KAZOOSH/solarbird/circuit/Solaranimal210527_2049/SolaranimalCircuit.png

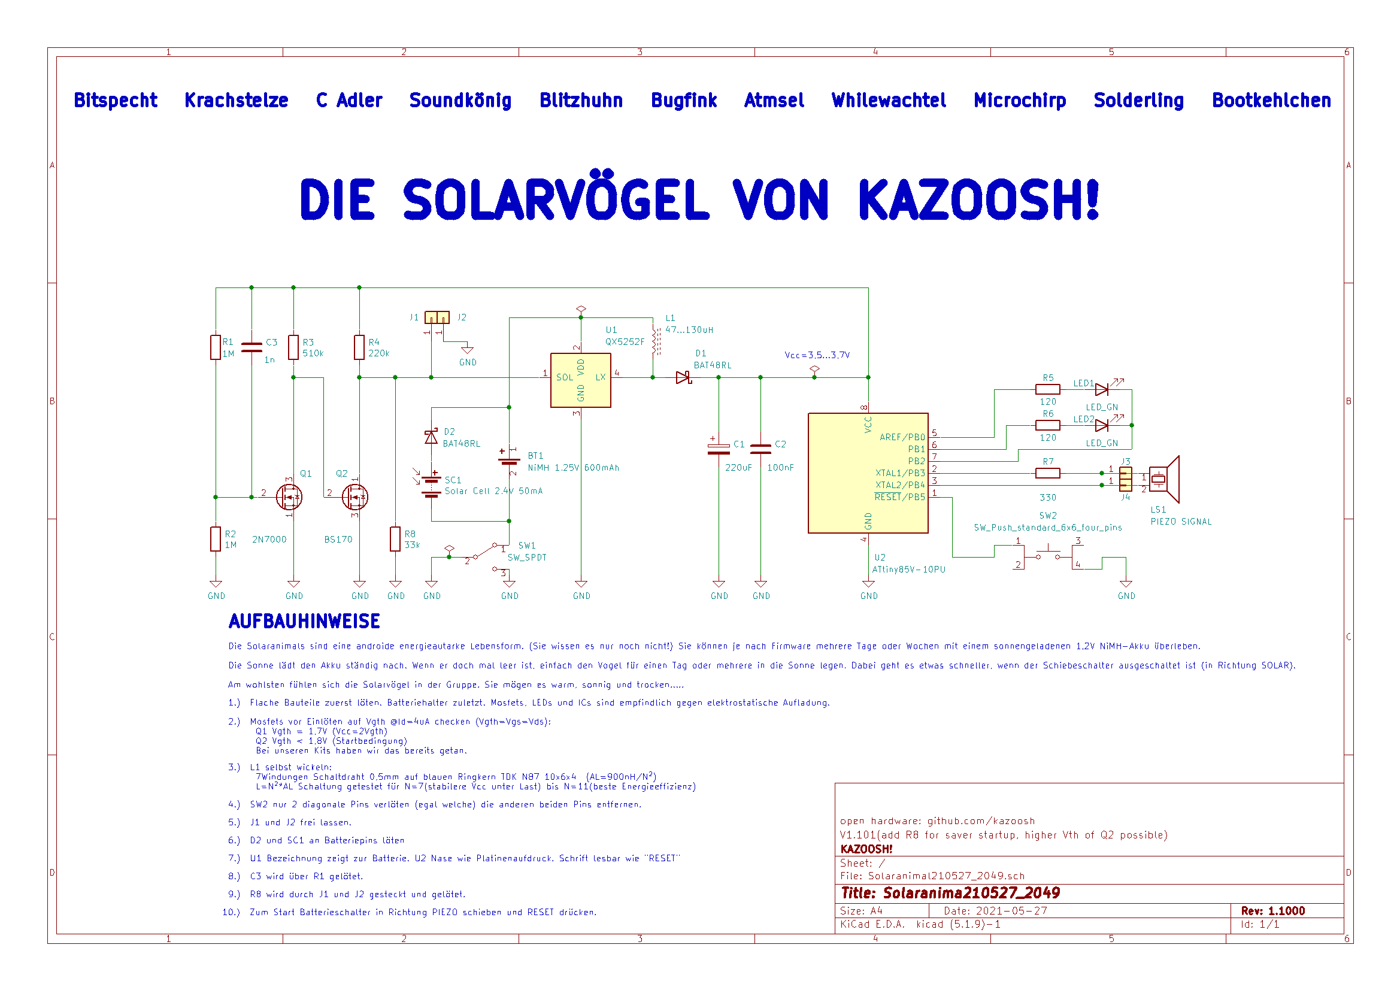
circuit/Solaranimal210527_2049/SolaranimalCircuit.png
