KAZOOSH/solarbird/circuit/spice/circuit.png

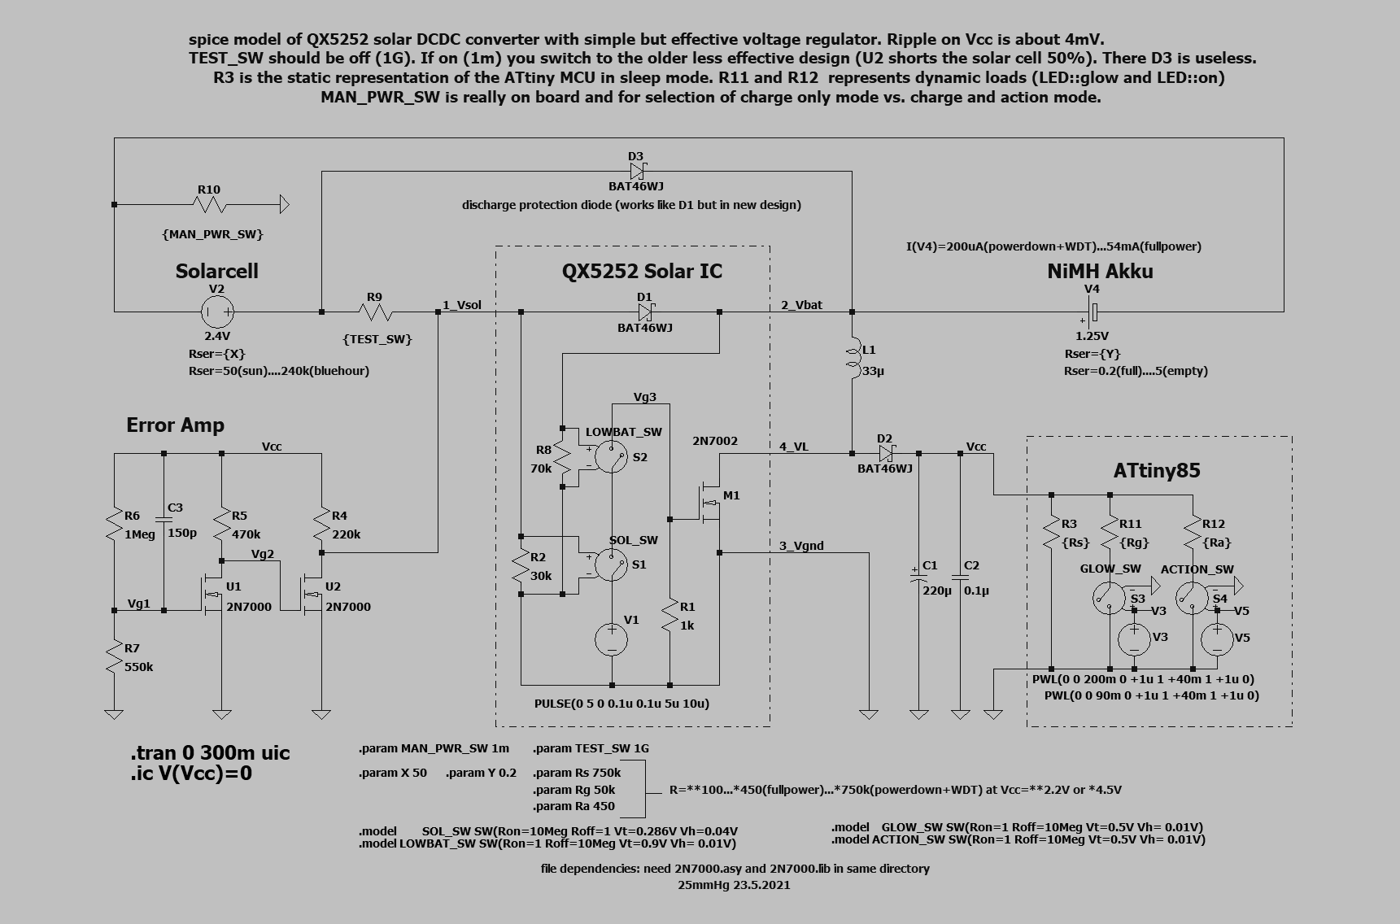
circuit/spice/circuit.png
