KAZOOSH/solarbird/pcb/Solaranimal_current pcb/board_b.png

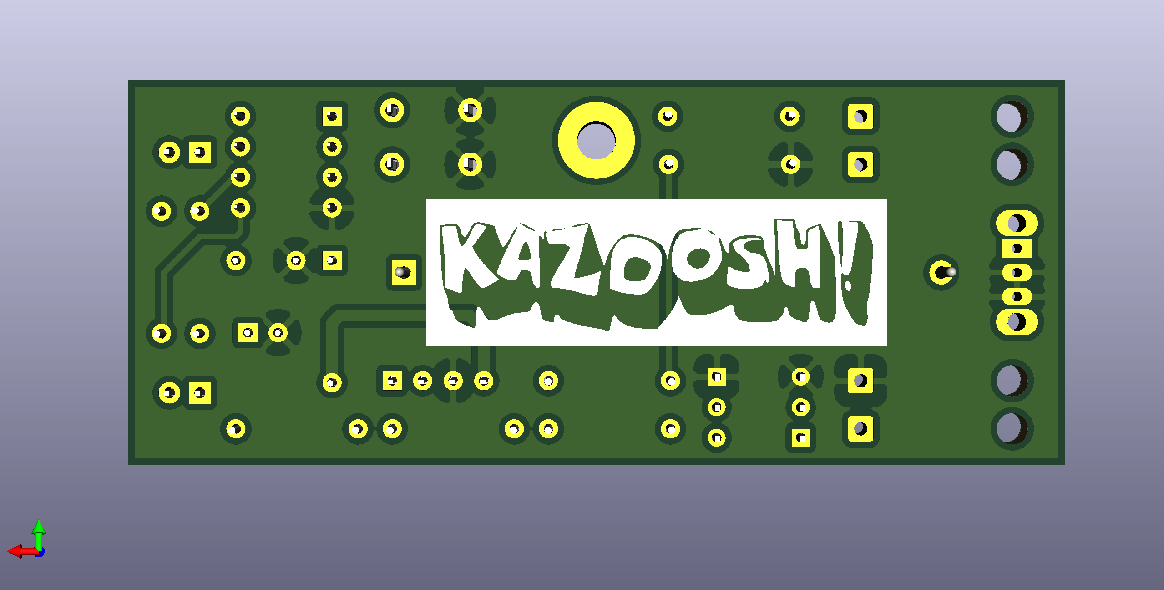
pcb/Solaranimal_current pcb/board_b.png
