KAZOOSH/solarbird/pcb/Solaranimal_current pcb/board_f.png

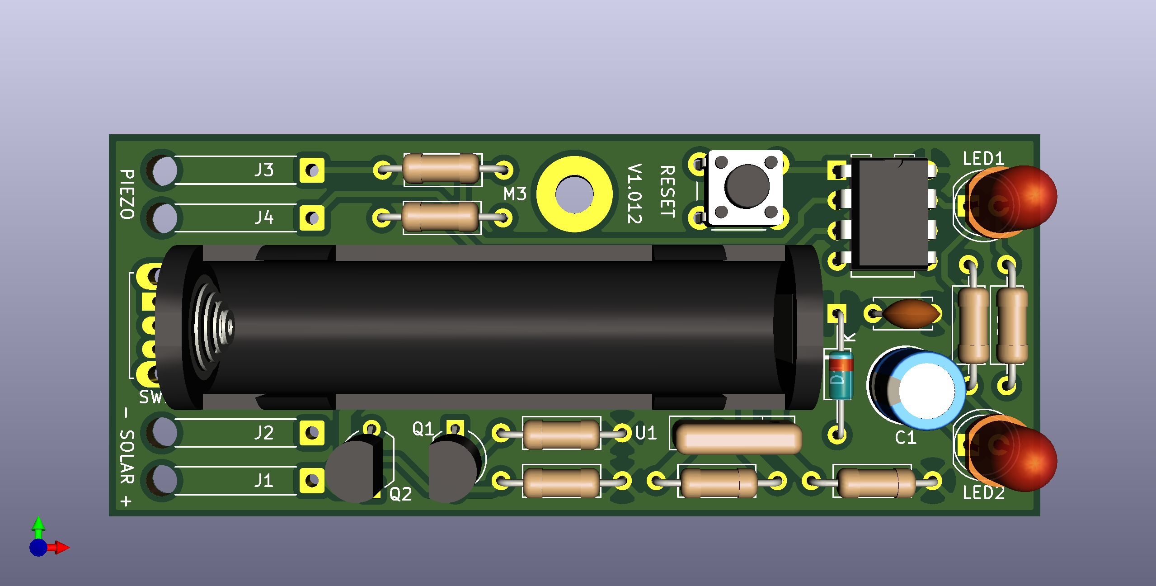
pcb/Solaranimal_current pcb/board_f.png
