KAZOOSH/solarbird/pcb/Solaranimal_current pcb/board_s.png

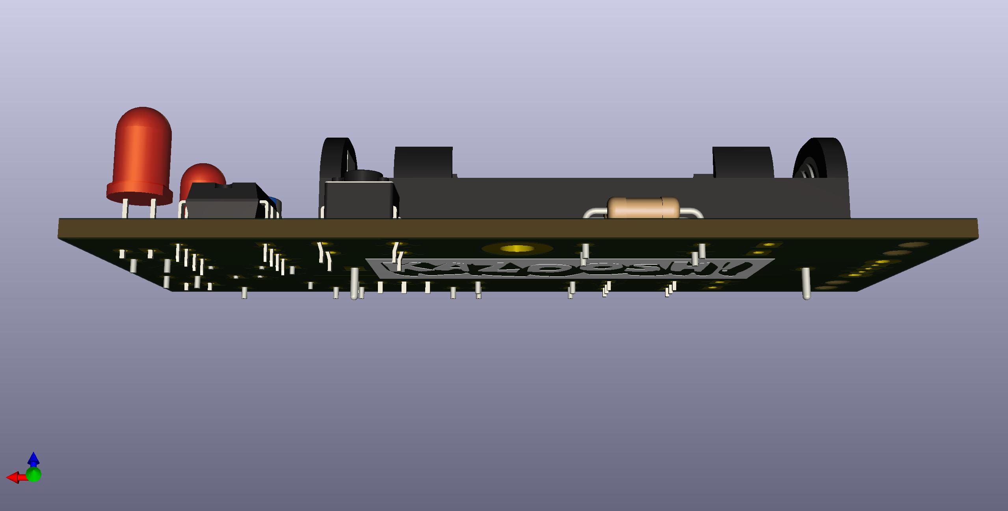
pcb/Solaranimal_current pcb/board_s.png
