KAZOOSH/solarbird/pcb/Solaranimal_current pcb/circuit.png

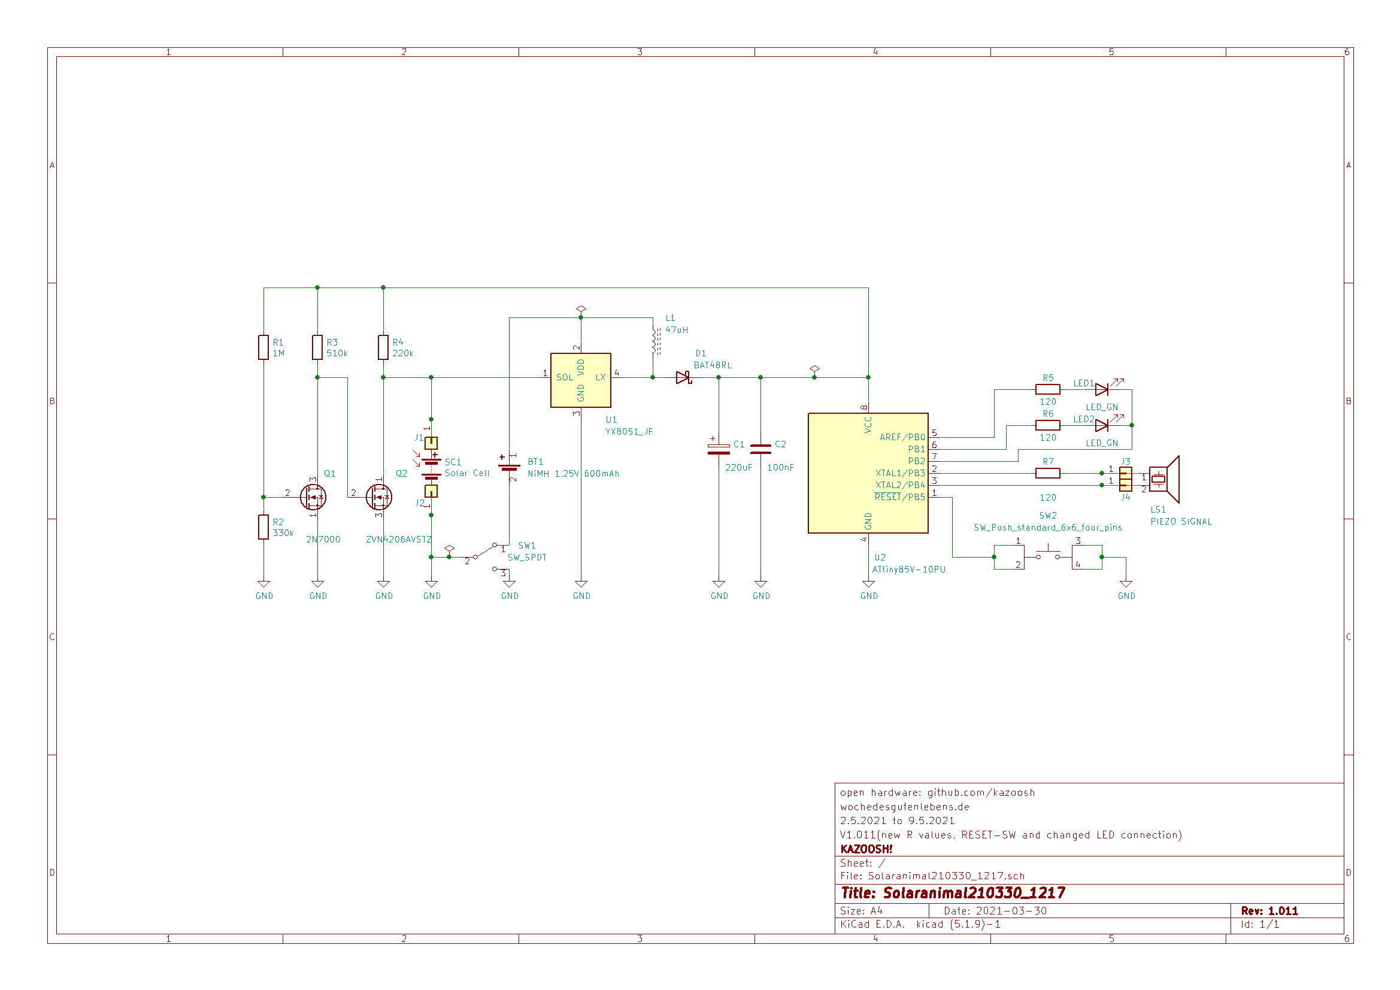
pcb/Solaranimal_current pcb/circuit.png
