KAZOOSH/solarbird/pcb/Solaranimal_current pcb/dimensions.png

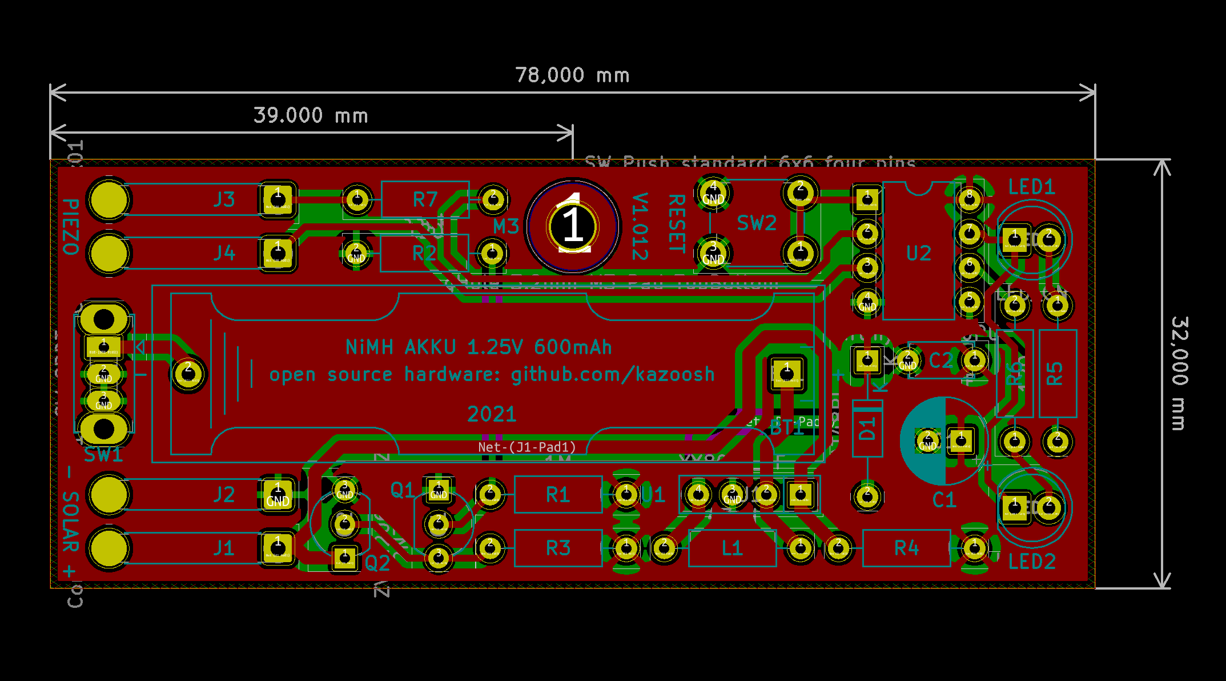
pcb/Solaranimal_current pcb/dimensions.png
