KAZOOSH/solarbird/material/capsense.png

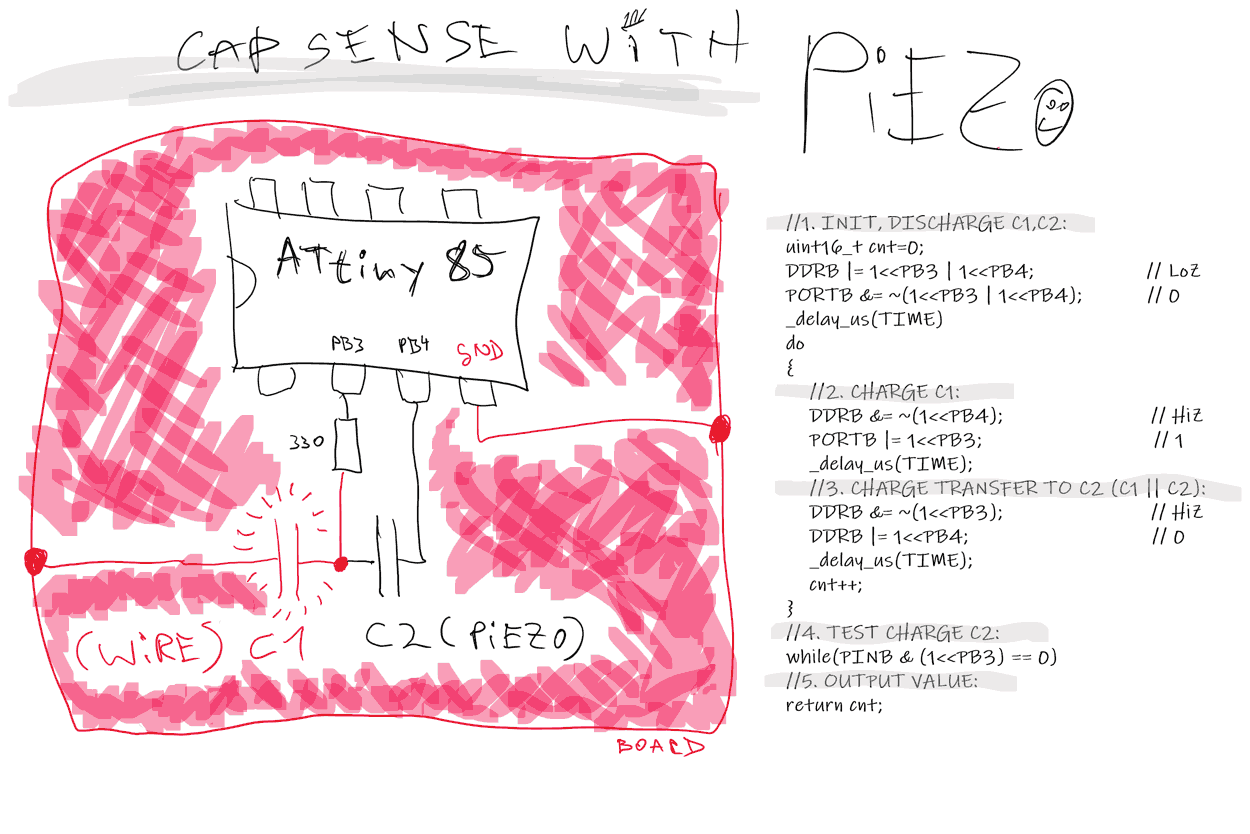
material/capsense.png
