KAZOOSH/solarbird/material/cicadas_waves/1_cicadas_envelope.jpg

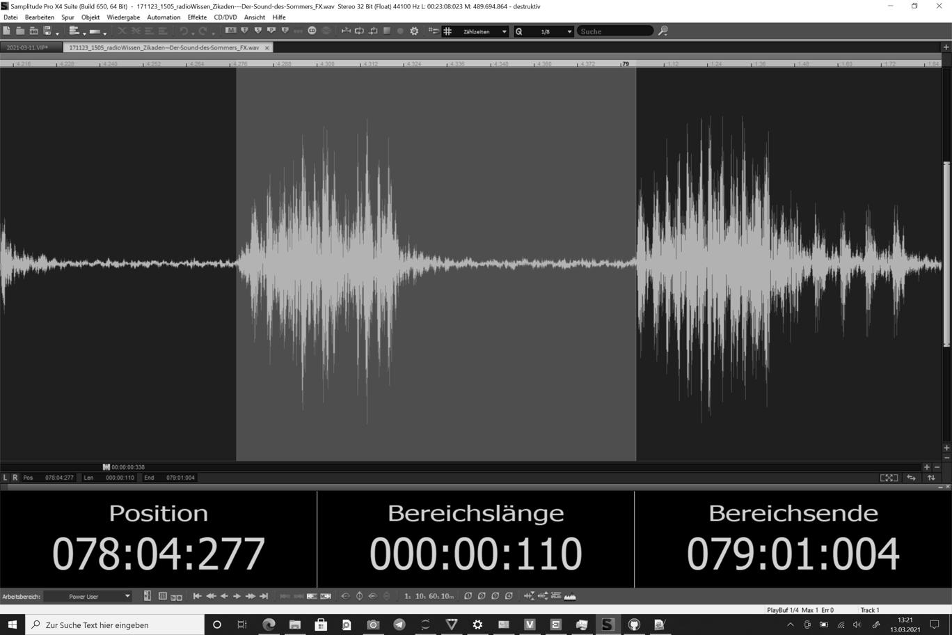
material/cicadas_waves/1_cicadas_envelope.jpg
