KAZOOSH/solarbird/material/cicadas_waves/2_cicadas_envelope_detail.jpg

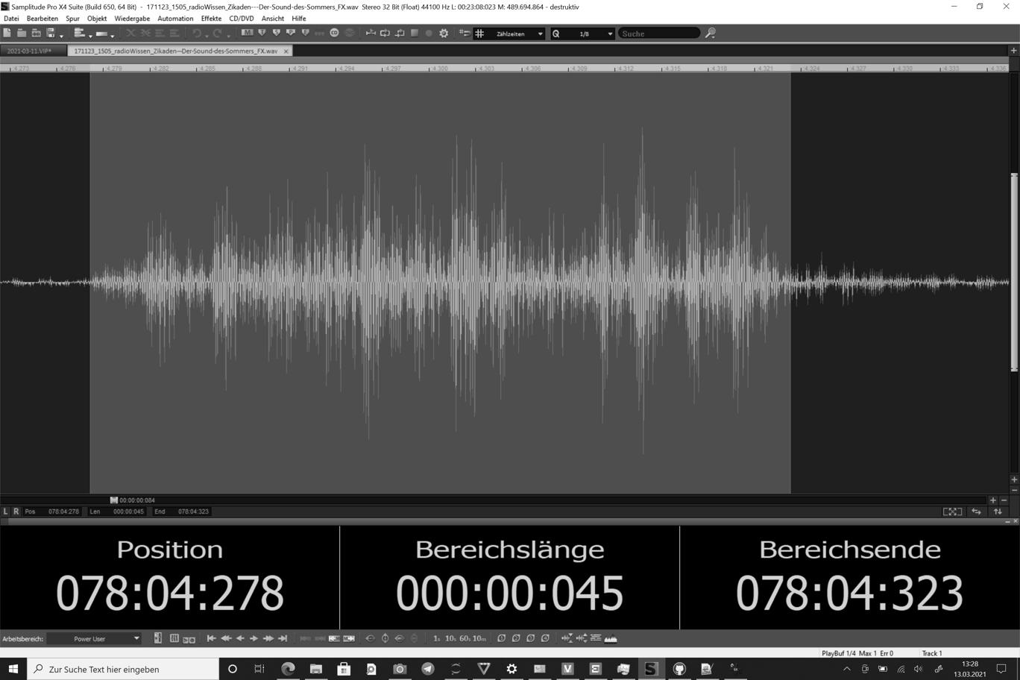
material/cicadas_waves/2_cicadas_envelope_detail.jpg
