KAZOOSH/solarbird/material/cicadas_waves/3_cicadas_3cycles.jpg

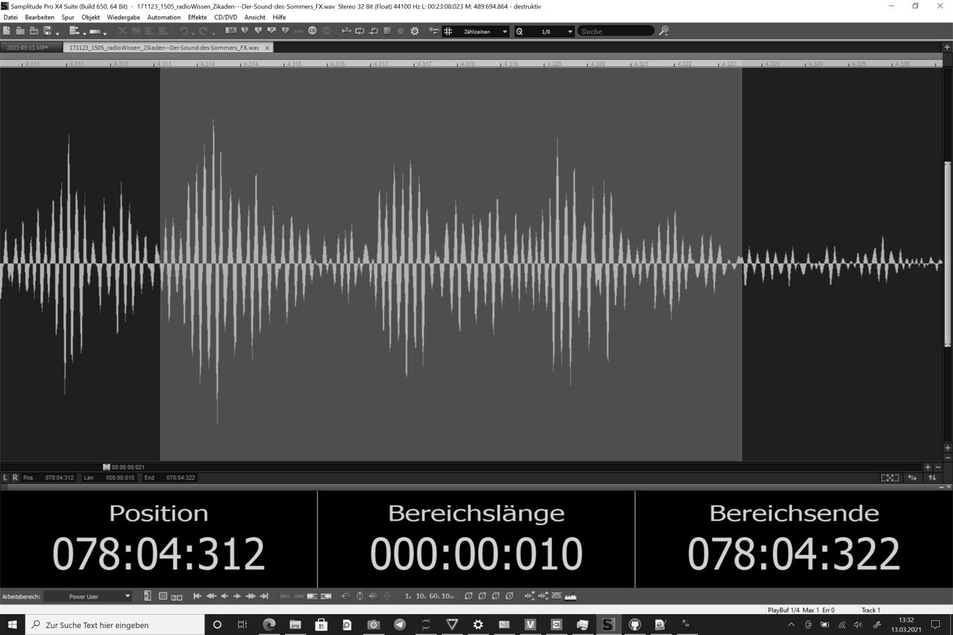
material/cicadas_waves/3_cicadas_3cycles.jpg
