KAZOOSH/solarbird/material/cicadas_waves/4_cicadas_cycle_with_samples.jpg

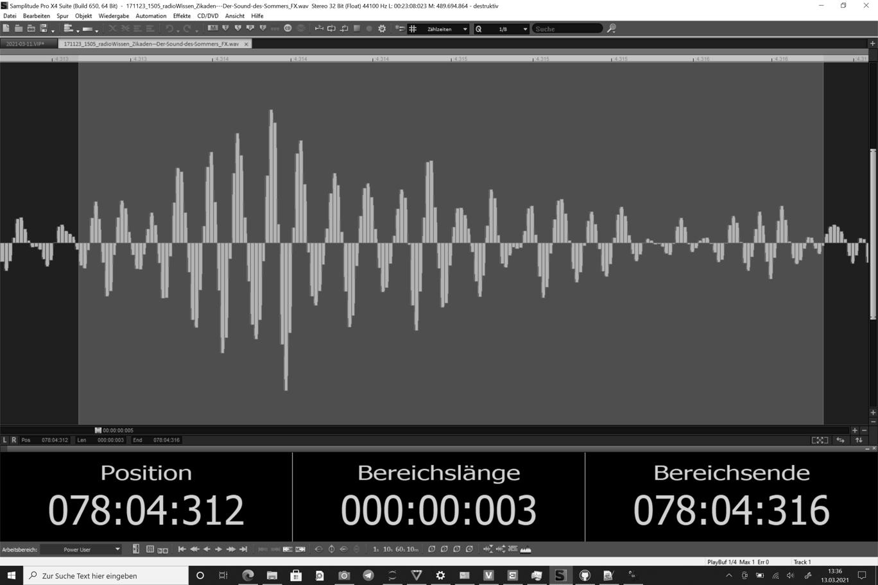
material/cicadas_waves/4_cicadas_cycle_with_samples.jpg
