KAZOOSH/solarbird/material/pwrsolution1.png

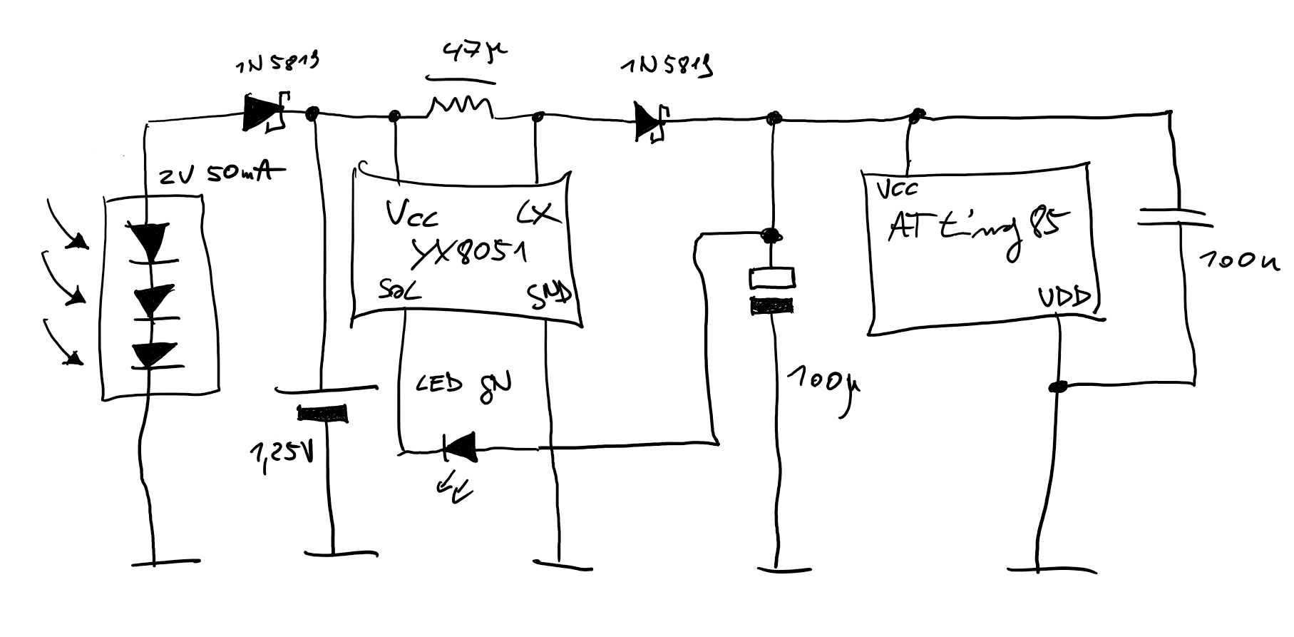
material/pwrsolution1.png
