KAZOOSH/solarbird/material/pwrsolution4.png

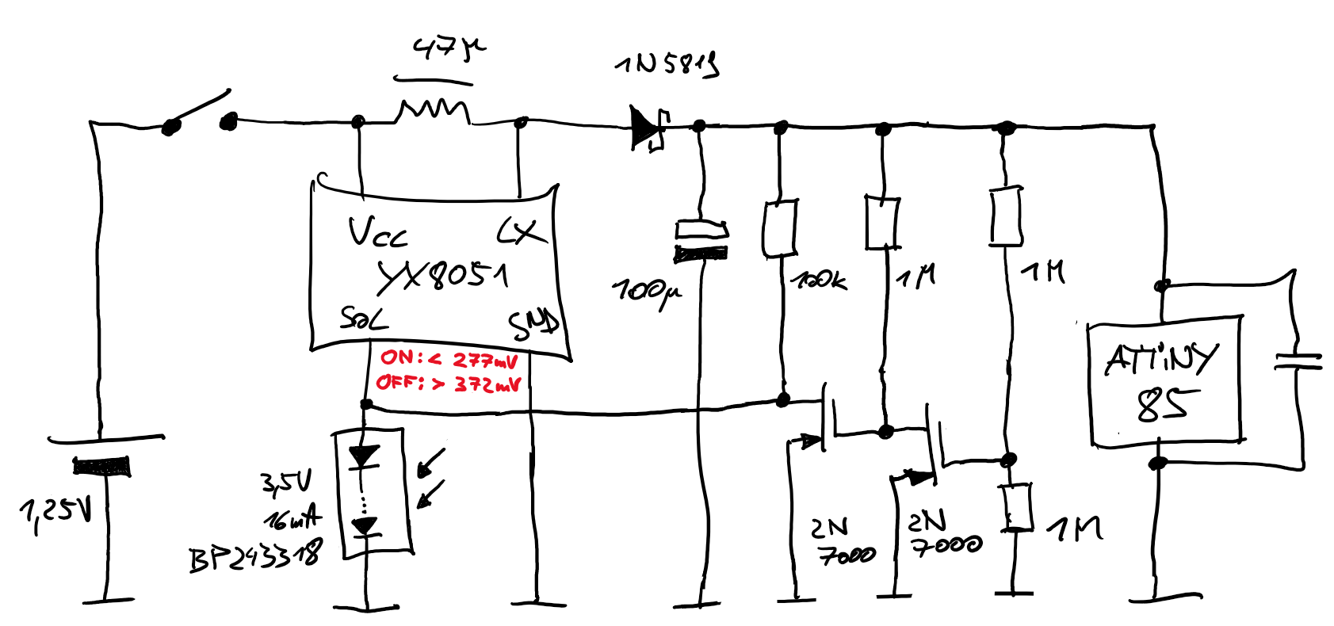
material/pwrsolution4.png
