KAZOOSH/solarbird/circuit/spice/ErrorAmpACDC.asc

C1: cap; {C}
R1: res; {R}
R2: res; 470k
R3: res; 1Meg
R4: res; 550k
R5: res; 30k
U1: 2N7000
U2: 2N7000
V2: voltage; AC 1
Named nets: 0, Vcc, Vg1, Vg2, out
Error Amp
.ac oct 12 0.1 1G
.op V(Vcc)=4.5V
.step param C list 0 33p 100p 330p
.dc V2 0 5
.step param R list 220k 270k 330k
inside
QX5252
