KAZOOSH/solarbird/circuit/spice/Solarbird.asc

C1: polcap; 220µ; V=4 Irms=3.72678 Rser=0.018 Lser=0 mfg="KEMET" pn="A700D107M004ATE018" type="Al electrolytic"
C2: cap; 0.1µ; V=16 Irms=4.39 Rser=0.0357547 Lser=0 mfg="KEMET" pn="C0402C104K4RAC" type="X7R"
C3: cap; 150p
D1: schottky; BAT46WJ
D2: schottky; BAT46WJ
D3: schottky; BAT46WJ
L1: ind; 33µ; Rser=0.01
M1: nmos; 2N7002
R1: res; 1k
R2: res; 30k
R3: res; {Rs}
R4: res; 220k
R5: res; 470k
R6: res; 1Meg
R7: res; 550k
R8: res; 70k
R9: res; {TEST_SW}
R10: res; {MAN_PWR_SW}
R11: res; {Rg}
R12: res; {Ra}
S1: sw; SOL_SW
S2: sw; LOWBAT_SW
S3: sw; GLOW_SW
S4: sw; ACTION_SW
U1: 2N7000
U2: 2N7000
V1: voltage; PULSE(0 5 0 0.1u 0.1u 5u 10u)
V2: voltage; 2.4V; Rser={X}
V3: voltage; PWL(0 0 200m 0 +1u 1 +40m 1 +1u 0)
V4: cell; 1.25V; Rser={Y}
V5: voltage; PWL(0 0 90m 0 +1u 1 +40m 1 +1u 0)
Named nets: 2_Vbat, 4_VL, 1_Vsol, 3_Vgnd, 0, Vcc, Vg1, Vg2, Vg3, V3, V5
.model        SOL_SW SW(Ron=10Meg Roff=1 Vt=0.286V Vh=0.04V
QX5252 Solar IC
.tran 0 300m uic
.param X 50
NiMH Akku
Solarcell
ATtiny85
.ic V(Vcc)=0
.model LOWBAT_SW SW(Ron=1 Roff=10Meg Vt=0.9V Vh= 0.01V)
Rser=0.2(full)....5(empty)
Rser=50(sun)....240k(bluehour)
.param Y 0.2
.param Rs 750k
R=**100...*450(fullpower)...*750k(powerdown+WDT) at Vcc=**2.2V or *4.5V
I(V4)=200uA(powerdown+WDT)...54mA(fullpower)
.param MAN_PWR_SW 1m
.param TEST_SW 1G
spice model of QX5252 solar DCDC converter with simple but effective voltage regulator. Ripple on Vcc is about 4mV.
TEST_SW should be off (1G). If on (1m) you switch to the older less effective design (U2 shorts the solar cell 50%). There D3 is useless.                       
     R3 is the static representation of the ATtiny MCU in sleep mode. R11 and R12  represents dynamic loads (LED::glow and LED::on)
                           MAN_PWR_SW is really on board and for selection of charge only mode vs. charge and action mode.
discharge protection diode (works like D1 but in new design)
Error Amp
.param Rg 50k
.param Ra 450
.model    GLOW_SW SW(Ron=1 Roff=10Meg Vt=0.5V Vh= 0.01V)
.model ACTION_SW SW(Ron=1 Roff=10Meg Vt=0.5V Vh= 0.01V)
file dependencies: need 2N7000.asy and 2N7000.lib in same directory
25mmHg 23.5.2021
