KAZOOSH/solarbird/circuit/Solaranimal210527_2049/Solaranimal210527_2049.sch

## KiCad design circuit/Solaranimal210527_2049/Solaranimal210527_2049.sch (2021-06-29)

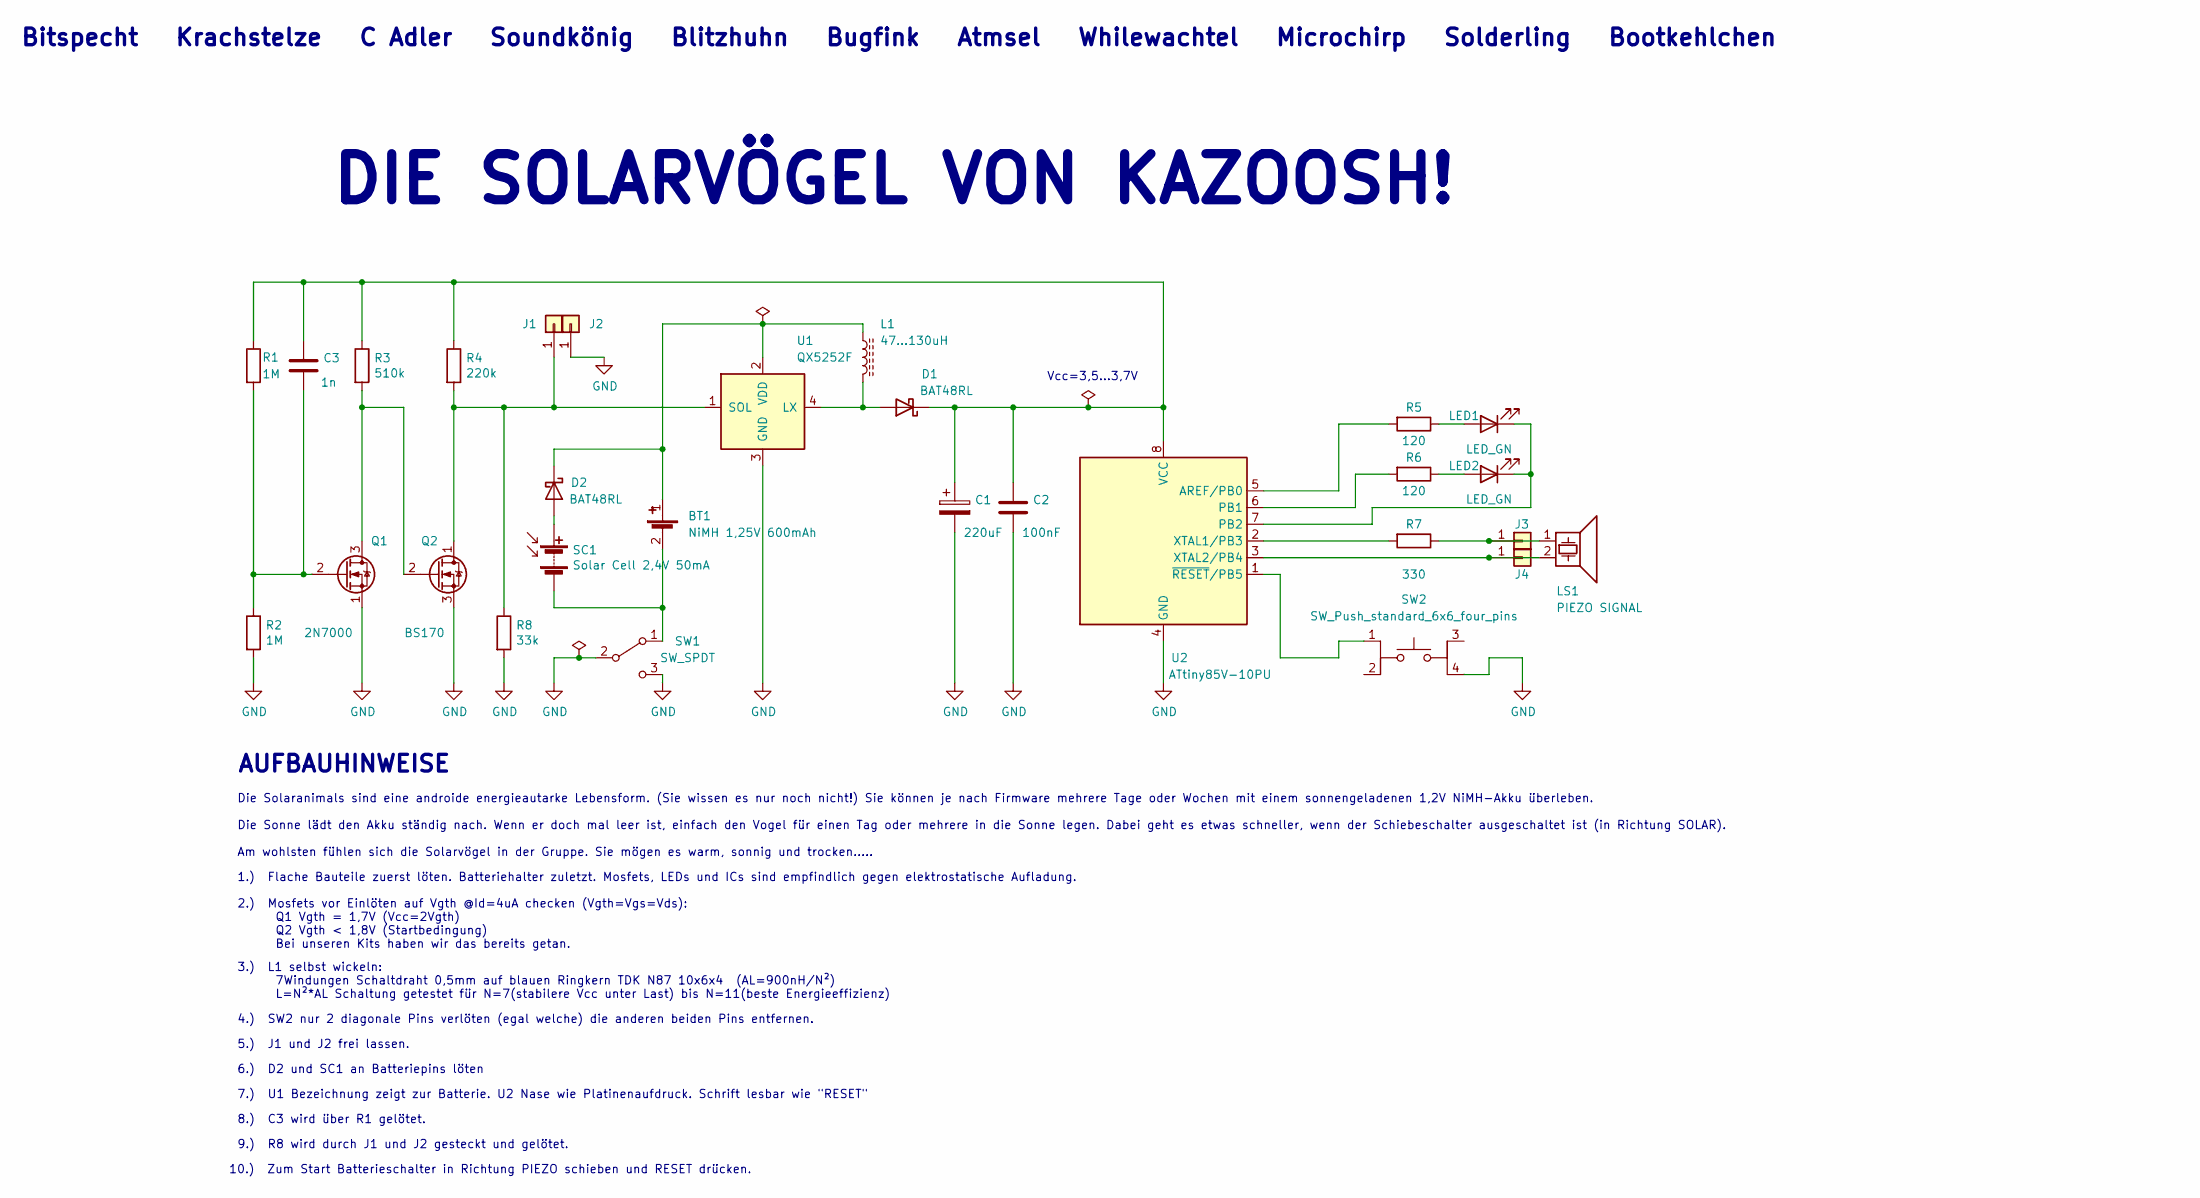
[picture p26: schematic Solaranimal210527_2049.sch]

Parts:
BT1: NiMH 1,25V 600mAh; BatteryHolder_Keystone_2466_1xAAA
C1: 220uF; CP_Radial_D6.3mm_P2.50mm
C2: 100nF; C_Disc_D4.7mm_W2.5mm_P5.00mm
C3: 1n; C_Disc_D4.7mm_W2.5mm_P5.00mm
D1, D2: BAT48RL; D_DO-35_SOD27_P10.16mm_Horizontal
J1, J2, J3, J4: Conn_01x01; SolderWire-0.5sqmm_1x01_D0.9mm_OD2.1mm_Relief
L1: 47...130uH; R_Axial_DIN0207_L6.3mm_D2.5mm_P10.16mm_Horizontal
LED1, LED2: LED_GN; LED_D5.0mm
LS1: PIEZO SIGNAL
Q1: 2N7000; TO-92_Inline_Wide
Q2: BS170; TO-92_Inline_Wide
R1, R2: 1M; R_Axial_DIN0207_L6.3mm_D2.5mm_P10.16mm_Horizontal
R3: 510k; R_Axial_DIN0207_L6.3mm_D2.5mm_P10.16mm_Horizontal
R4: 220k; R_Axial_DIN0207_L6.3mm_D2.5mm_P10.16mm_Horizontal
R5, R6: 120; R_Axial_DIN0207_L6.3mm_D2.5mm_P10.16mm_Horizontal
R7: 330; R_Axial_DIN0207_L6.3mm_D2.5mm_P10.16mm_Horizontal
R8: 33k; R_Axial_DIN0207_L6.3mm_D2.5mm_P10.16mm_Horizontal
SC1: Solar Cell 2,4V 50mA
SW1: SW_SPDT; SW_Slide_1P2T_CK_OS102011MS2Q
SW2: SW_Push_standard_6x6_four_pins; SW_PUSH_6mm_H5mm_4pin
U1: QX5252F
U2: ATtiny85V-10PU; DIP-8_W7.62mm

Connections:
GND: C1.2, C2.2, J2.1, Q1.1 (S), Q2.3 (S), R2.2, R8.2, SW1.2 (B), SW1.3 (C), SW2.4, U1.3 (GND), U2.4 (GND)
unnamed: BT1.1 (-), D2.1 (K), L1.1, U1.2 (VDD)
unnamed: BT1.2 (plus), SC1.2 (-), SW1.1 (A)
unnamed: C1.1, C2.1, C3.1, D1.1 (K), R1.1, R3.1, R4.1, U2.8 (VCC)
unnamed: C3.2, Q1.2 (G), R1.2, R2.1
unnamed: D1.2 (A), L1.2, U1.4 (LX)
unnamed: D2.2 (A), SC1.1 (+)
unnamed: J1.1, Q2.1 (D), R4.2, R8.1, U1.1 (SOL)
unnamed: J3.1, LS1.1, R7.1
unnamed: J4.1, LS1.2, U2.3 (XTAL2/PB4)
unnamed: LED1.1 (K), LED2.1 (K), U2.7 (PB2)
unnamed: LED1.2 (A), R5.1
unnamed: LED2.2 (A), R6.1
unnamed: Q1.3 (D), Q2.2 (G), R3.2
unnamed: R5.2, U2.5 (AREF/PB0)
unnamed: R6.2, U2.6 (PB1)
unnamed: R7.2, U2.2 (XTAL1/PB3)
unnamed: SW2.1, U2.1 (~RESET~/PB5)

Notes on the sheet:
2.) Mosfets vor Einlöten auf Vgth @Id=4uA checken (Vgth=Vgs=Vds): Q1 Vgth = 1,7V (Vcc=2Vgth) Q2 Vgth < 1,8V (Startbedingung) Bei unseren Kits haben wir das bereits getan.
3.) L1 selbst wickeln: 7Windungen Schaltdraht 0,5mm auf blauen Ringkern TDK N87 10x6x4 (AL=900nH/N²) L=N²*AL Schaltung getestet für N=7(stabilere Vcc unter Last) bis N=11(beste Energieeffizienz)
5.) J1 und J2 frei lassen.
Vcc=3,5...3,7V
6.) D2 und SC1 an Batteriepins löten
4.) SW2 nur 2 diagonale Pins verlöten (egal welche) die anderen beiden Pins entfernen.
AUFBAUHINWEISE
7.) U1 Bezeichnung zeigt zur Batterie. U2 Nase wie Platinenaufdruck. Schrift lesbar wie "RESET"
1.) Flache Bauteile zuerst löten. Batteriehalter zuletzt. Mosfets, LEDs und ICs sind empfindlich gegen elektrostatische Aufladung.
9.) R8 wird durch J1 und J2 gesteckt und gelötet.
Die Solaranimals sind eine androide energieautarke Lebensform. (Sie wissen es nur noch nicht!) Sie können je nach Firmware mehrere Tage oder Wochen mit einem sonnengeladenen 1,2V NiMH-Akku überleben. Die Sonne lädt den Akku ständig nach. Wenn er doch mal leer ist, einfach den Vogel für einen Tag od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
DIE SOLARVÖGEL VON KAZOOSH!
Bitspecht Krachstelze C Adler Soundkönig Blitzhuhn Bugfink Atmsel Whilewachtel Microchirp Solderling Bootkehlchen
8.) C3 wird über R1 gelötet.
10.) Zum Start Batterieschalter in Richtung PIEZO schieben und RESET drücken.
