KAZOOSH/solarbird/test/T85MichisVogel/T85MichisVogel/main.c

/*
 * T85MichisVogel.c
 *
 * Created: 01.05.2021 11:47:39
 * Author : 25mmHg
 * Fuses: lfuse=c2, hfuse=DF, efuse=FF
 *
 *    .--------------------------------------------.
 *    |       _______                              |
 *    |      | YX805 |                             |
 *    |      | _ _ _ |                             |
 *    |     1 o o o o 4                            |
 *    |       | | | |                              |
 *    '-------' | | |                              |
 *    .---------' | |  BAT48                       |
 *    |    ___    | |                              |
 *    o----UUU----)-o--->|--o------o-------o-------)---------------o-----o--------------o--------.
 *    |           |         |      |       |       |               |     |              |        |
 *    |    60u    |        .-.    .-.     .-.      |               |     |      PIEZO   |        |
 *    |           |        | |    | |     | |      |               |     |        _     |        |
 *    |           |        | |    | |     | |      |               |     |       | |    |        |  2x 200R  2x GN LED
 *    |           |      1M'-'470k'-' 220k'-'      |          220u | +   |    .-|| ||-. |ATtiny85|
 *    |           |         |      |       o-------o              ###   ---   |  |_|  | | 1 __ 8 | .---------------.
 *    |           |         |   ||-o--. ||-+       |              ---   ---   |       | '-o|  |o-' |               |
 *    |   |       |         |   ||<-  | ||<-      .-.              | 100n|    |       '---o|  |o---'  ___          |
 *    '---| |-----o         o---||-+  '-||-+      | |              |     |    |       .---o|  |o-----|___|-->|-----o
 *     +  |   -   |         |2N7000|ZVN4206|      | | 62R          |     |    |       | .-o|__|o---.               |
 *                |        .-.     |       |      '-'              |     |    |  ___  | |          |  ___          |
 *       Ni-MH    |        | |     |       |       |               |     |    '-|___|-' |          '-|___|-->|-----'
 *       1,25V    |        | |     |       |       |               |     |              |
 *       600mAh   |    650k'-'     |       |       V SOLARZELLE    |     |       200    |
 *                |         |      |       |       - 2,5V 50mA     |     |              |
 *                |         |      |       |       |               |     |              |
 *               ---       ---    ---     ---     ---             ---   ---            ---
 *
 * (created by AACircuit v1.28.7 beta 10/23/16 www.tech-chat.de)
 *
 */ 

#define F_CPU 8000000UL
#define MAXDARKNESS 10000UL

#define PIEPA PB3
#define PIEPB PB4
#define LEDANODE1 PB0
#define LEDANODE2 PB1
#define LEDKATHODES PB2
#define MYDDR DDRB
#define MYPORT PORTB
#define MYPIN PINB

#include <avr/io.h>
#include <avr/sleep.h>
#include <avr/wdt.h>
#include <avr/interrupt.h>
#include <util/delay.h>

volatile uint16_t wdtcnt = 0;

//Variable delay
void var_delay_10us(uint16_t ten_us)
{
	for (uint16_t i=0; i<ten_us; i++) _delay_us(10);
}

//Pieps
void piepsen(uint16_t n, uint16_t t)
{
	MYDDR  |=  ((1<<PIEPA) | (1<<PIEPB));
	MYPORT |=  (1<<PIEPA);
	MYPORT &= ~(1<<PIEPB);
	while(n)
	{
		n--;
		MYPIN |= ((1<<PIEPB) | (1<<PIEPA));
		var_delay_10us(t);
	}
	MYPORT &= ~((1<<PIEPA) | (1<<PIEPB));
	_delay_us(10);
	// PINSTATE: booth piezopins are GND
}

 //How dark is it
uint16_t get_darkness()
{
	uint16_t darkness = 0;
	//booth junctions invers charging
	MYDDR  |=  ((1<<LEDANODE1) | (1<<LEDANODE2) | (1<<LEDKATHODES));
	MYPORT &= ~((1<<LEDANODE1) | (1<<LEDANODE2));
	MYPORT |=  (1<<LEDKATHODES);
	_delay_us(10);
	//discharge junctions to HIGH
	MYDDR &= ~((1<<LEDANODE1 | 1<<LEDANODE2));
	while(!(MYPIN & ((1<<LEDANODE1) | (1<<LEDANODE2))) && (darkness < MAXDARKNESS))
	{
		darkness++;
		_delay_us(10);
	}
	MYPORT &= ~(1<<LEDKATHODES);
	MYPORT &= ~((1<<LEDANODE1) | (1<<LEDANODE2));
	MYDDR  |=  ((1<<LEDANODE1) | (1<<LEDANODE2) | (1<<LEDKATHODES));
	return(darkness);
	// PINSTATE: anodes are GND, kathodes are GND
}

 //Flash the LEDs
 void flash_leds(uint16_t ontime)
 {
	 MYDDR  |= ((1<<LEDANODE1) | (1<<LEDANODE2) | (1<<LEDKATHODES));
	 MYPORT &= ~(1<<LEDKATHODES);
	 MYPORT |= ((1<<LEDANODE1) | (1<<LEDANODE2));
	 var_delay_10us(ontime);
	 MYPORT &= ~((1<<LEDANODE1) | (1<<LEDANODE2));
	 // PINSTATE: anodes are GND, kathodes are GND
 }


// WDT-Interrupt-init
// START 8s TIMER, current is 6uA
void init_wdt()
{
	cli();
	MCUSR &= ~(1<<WDRF);
	WDTCR |= ((1<<WDIE) | (1<<WDP3) | (1<<WDP0)) ;
	wdt_reset();
	sei();
}


// WDT-Interrupt, w<keup from sleeping without RESET
ISR(WDT_vect)
{
	wdtcnt++;
}

int main(void)
{
    // init
	MYDDR |= ((1<<PIEPA) | (1<<PIEPB));
	MYDDR |= (1<<LEDKATHODES);
	
	// LOWLIGHT LEDs VIA PULLUP
	MYPORT |= (1<<LEDANODE1);
	MYPORT |= (1<<LEDANODE2);
	_delay_ms(1000);
	MYPORT &= ~(1<<LEDANODE1);
	MYPORT &= ~(1<<LEDANODE2);
	// PINSTATE: anodes, kathodes and piezopins are GND
	
	set_sleep_mode(SLEEP_MODE_PWR_DOWN);
	init_wdt();
		
	// Job	
	while(1) 
    {
		// Test Light Sensors
		if (wdtcnt == 1)
		{
			for (uint16_t i=0; i<200; i++)
			{
				piepsen(10, (5+(get_darkness()>>3)));
			}			
		}   
		
		else if (wdtcnt & 1 || wdtcnt & 2);
		
		else if (wdtcnt & 4U)
		{
			piepsen(300, 8);
			flash_leds(get_darkness());
			piepsen(400, 6);
		}
		
		else if (wdtcnt & 8U)
		{
			// make noise filtered with 2 LFSR (flanger)
			MYDDR  |=  ((1<<PIEPA) | (1<<PIEPB));
			MYPORT |=  (1<<PIEPA);
			MYPORT |=  (1<<PIEPB); // Differenz AB
			//MYPORT &= ~(1<<PIEPB); // Summe AB alternativ
			uint16_t lfsr_stateA = 44257; // Startwert für A
			uint16_t lfsr_stateB = 38051; // Wert 100 Schritte vor A (B hat  hier 2,3ms Vorsprung vor A)
			for (uint16_t j=0; j<200; j++)
			{
				for (uint16_t k=0; k<300; k++)
				{
					_delay_us(23);
					// nach E.Galois
					lfsr_stateA=(lfsr_stateA >> 1)^(-(lfsr_stateA & 1) & 0xB400U);
					// jedes 300te Sample verpennen (Abstand A B variiert 2,3ms....0....2,3ms)
					if (k != 1) lfsr_stateB=(lfsr_stateB >> 1)^(-(lfsr_stateB & 1) & 0xB400U);
					// PowerMixer
					MYPIN |= ((lfsr_stateA & 1) << PIEPA) | ((lfsr_stateB & 1) << PIEPB);
				}
			}
			MYPORT &= ~((1<<PIEPA) | (1<<PIEPB));
			// PINSTATE: booth piezopins are GND
		}
		
		else if(wdtcnt & 16U)
		{
			piepsen(1000, 5);
			piepsen(25, 400);
			piepsen(50, 200);
			piepsen(100, 50);
			piepsen(200, 25);
			piepsen(500, 10);
			piepsen(600, 8);
			piepsen(700, 7);
			piepsen(800, 6);
			piepsen(1000, 20);
			piepsen(741, 27);
			piepsen(800, 6);
			piepsen(700, 7);
			piepsen(600, 8);
			piepsen(500, 10);
			piepsen(200, 25);
			piepsen(100, 50);
			piepsen(50, 200);
			piepsen(25, 400);
			piepsen(1000, 5);			
		}
		
		else if (wdtcnt & 32U)
		for (uint8_t i=0; i<4; i++)
		{
			piepsen(300, 80);
			piepsen(400, 60);
			piepsen(300, 80);
			_delay_ms(240);
			piepsen(300, 80);
			piepsen(400, 60);
			_delay_ms(960);
		}
		
		else;
		sei();
		sleep_mode();
		cli();
	}
}
